OSUrobotics/applevision_tof_profiler/data/Apple150mmNoBackdrop.png

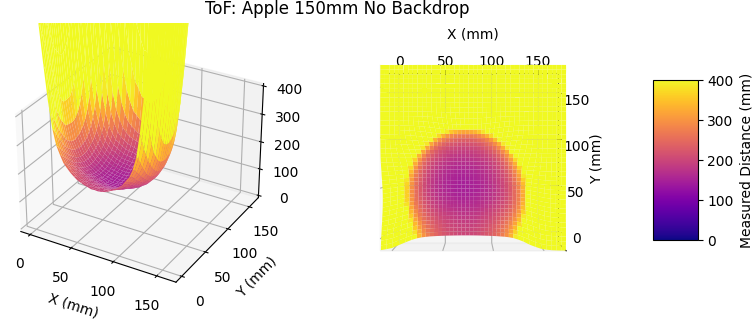
data/Apple150mmNoBackdrop.png
